pershin/pcm-player/software/player.h

/*
 * File:   player.h
 * Author: Sergey Pershin <sergey.pershin at hotmail.com>
 *
 * Created on May 8, 2020, 7:20 PM
 */

#ifndef PLAYER_H
#define PLAYER_H

#define F_CPU        16000000UL
#define BUFFER_SIZE  1024
#define BUFFER_CHUNK 512
#define SAMPLE_RATE  44100
#define COMMAND_NEXT 1
#define COMMAND_PREV 2

#endif /* PLAYER_H */
